facarvalho/MeetingHub-4/v2/docs/relatorio-validacao-v2.html

Dossiê de engenharia · Hardware

# MeetingHub-4 v2

Validação elétrica completa e autorização de fabricação da placa — roteador analógico de áudio/microfone para salas com 4 notebooks.

Revisão rev-10 Data 2026-09-04 Placa 2 camadas · 100% THT · 0 SMD Dimensões 192 × 156 mm Peças 121

AUTORIZADO PARA FABRICAÇÃO rev-10

Os 27 testes automatizados passam (21/21 elétricos + 8/8 seletor one-hot + 6/6 mixer/mudo + 7/7 transiente de comutação), confirmados em dois motores de simulação independentes — um solver MNA próprio e ngspice 41 com modelos de datasheet dos componentes reais da BOM. DRC da placa: 0 erros. As 3 falhas da v1 (que custaram R$ 3000) estão corrigidas e reverificadas. Liberação condicionada a 2 verificações de bancada no primeiro artigo (§9).

27/27

testes automatizados aprovados

0

erros de DRC · 0 pads não conectados

3/3

falhas da v1 corrigidas + reverificadas

2

motores de simulação concordam

## 1 · O equipamento

O MeetingHub-4 é uma caixa alimentada por USB-C que conecta um único headset a quatro notebooks em uma sala de reunião. O usuário ouve o áudio dos quatro laptops misturado (cada um com seu volume, mais um volume geral) e escolhe, por botão, para qual laptop o microfone do headset fala. Toda a comutação de microfone é feita por relés em lógica one-hot exclusiva (nunca dois ao mesmo tempo), e a placa liga sempre em mudo.

A arquitetura é deliberadamente analógica: um plugue TRRS não pode re-enumerar, entrar em suspend nem trocar o dispositivo padrão do Windows — que é exatamente a falha "o Windows perdeu meu headset no meio da call" que motivou o projeto. Não há firmware, não há USB de dados, nada para instalar.

Parâmetro | Valor (simulado / de projeto)
Alimentação | USB-C, somente VBUS · fusível PTC 500 mA (RXEF050) · TVS P6KE6.8A
Consumo total | 50,6 mA (10% do fusível) · só 1 relé energizado por vez
Entradas de laptop | 4 × TRRS 3,5 mm (PJ-3200B-4A, 100% THT)
Saída de headset | 1 × TRRS 3,5 mm (fone L/R + microfone electret)
Referência VBIAS | 2,5000 V · bufferizada (LM358) · Zsaída < 1 Ω
Mixer | NJM4580 somador inversor · −0,33×/canal · sem clip com 4 laptops em fase
Amp de fone | NJM4556A (70 mA) · ganho 2× · R16/R20 = 10 Ω série (rev-10)
Ganho monitor (carga 32 Ω) | 0,50× (−6 dB) · ~0,7 mW · ≈ 96 dB SPL em IEM
Resposta em frequência | −0,7 dB @ 100 Hz · plana até 20 kHz · −3 dB @ 44 Hz
Seletor de microfone | CD4043B (latch NOR) + matriz de 20 diodos + POR + 4 × 2N7000 → relés
Power-on reset | janela de mudo de 139 ms (garante boot em mudo mesmo com rampa lenta de VBUS)

## 2 · As três falhas da v1 — status na v2

A primeira fabricação (lote JLCPCB W2026080810364558) trouxe três erros de esquemático. Todos foram corrigidos na v2 e reverificados independentemente por simulação neste dossiê.

# | Falha da v1 | Correção na v2 | Reverificado em

1 | Potenciômetros de volume invertidos → direção errada, não zeravam | Sinal no terminal 3/6, VBIAS no 1/4. Full-CW = mais alto; full-CCW = silêncio. | §B2, §M — 80 dB de faixa
2 | Relés de mic K1–K4: bobina e contatos trocados → mic morto | Bobina = pinos 2 (+5 V) e 9 (dreno do MOSFET); D2–D5 freewheel corretos. Re-arquitetado one-hot. | §E, §G2 — exclusivo 8/8
3 | VBIAS sem buffer (10k/10k + 10 µF) → vazamento no volume mínimo | Buffer LM358 com realimentação após R38 → 2,5000 V exatos, < 1 Ω. | §A1–A4 — 0,5 mΩ

## 3 · Metodologia de simulação

LTspice é ferramenta Windows GUI e não roda neste ambiente headless. Foram usados dois motores independentes, com resultados que concordam em todos os números:

- Solver MNA próprio (simulation/scripts/mna.py) — análise nodal modificada com .op / .ac / .tran, solves complexos exatos sem erro de passo temporal. Cobre §A–§M (ganho, mudo, resposta, impedância).
- ngspice 41 com modelos de datasheet dos componentes reais da BOM — macromodelos de 2 polos para NJM4580 / NJM4556A / LM358 (GBW, slew, Avol, Vsat-vs-trilho, Iq), 1N4148, 2N7000 (VTO 2,1 V, Rds(on) 1,8 Ω), P6KE6.8A, CD4043B (modelo comportamental de latch NOR, limiares CD4000B em 5 V), relé G5V-1 (167 Ω + L, contato comutado). Netlists em simulation/spice/*.cir.
- Lógica one-hot — simulação de eventos construída diodo a diodo a partir do netlist (select_logic.py).
- Cada bloco também tem netlist LTspice equivalente em simulation/ltspice/ para reproduzir os números em LTspice real.

Valores e conectividade vêm de hardware/PCB/MeetingHub-4-v2.net e das folhas KiCad POWER / MIXER / HPAMP / SELECT_LOGIC — não do texto de projeto. Toolchain reprodutível: bash /home/fac/.simtools/regen_sim.sh.

## 4 · Placar de resultados

21/21

§A–§G · elétrico idealizado (MNA)

8/8

§E · sequência do seletor one-hot

6/6

§M · mixer / "volume zero é silêncio"

7/7

§O · comutar mic não interrompe o monitor

✓

§N · ngspice + modelos reais bate com MNA

1,25 V

§P · laptop deselecionado ainda "vê" o mic

### Resultados por bloco (§A–§G, motor MNA)

# | Requisito | Medido

A1 | VBIAS = 2,50 V | 2,5000 V | OK
A2 | Zsaída < 1 Ω (degrau de carga DC) | 0,5 mΩ | OK
A3/A4 | Zout < 1 Ω @ 1 kHz · < 5 Ω @ 20 kHz | 48 mΩ · 0,86 Ω | OK
B1 | ganho de sistema (nota de projeto ≈ 0,66×) | 0,659× sem carga · 0,50× (−6 dB) em 32 Ω (rev-10) | OK
B2 | direção do pote: CW alto, full-CCW = mudo | faixa ≥ 66 dB CW-vs-CCW | OK
B3 | 100 Hz – 20 kHz plano ±1 dB | −0,7 dB @ 100 Hz · +0,0 dB @ 20 kHz | OK
B4 | extensão de graves | −3 dB @ 44 Hz · −10 dB @ 20 Hz (ok para voz) | OK
C1 | ganho por canal −0,33 (−3k3/10k) | 0,330× | OK
C2/C3 | sem clip: 1 laptop · 4 laptops em fase (pior caso) | 0,15 Vpk · 0,59 Vpk / ±1,3 V (45%) | OK
D1 | ganho do amp de fone antes da rede de saída | 1,52× após divisor 10 Ω/32 Ω (rev-10) | OK
D2 | sem DC no fone (C17 bloqueia) | 0,0 mV | OK
D3 | cap de saída suficiente (C17 = 220 µF) | 22,6 Hz para C17/32 Ω | OK
D4 | > 0,5 mW em 32 Ω de uma fonte −10 dBV | 0,65–0,79 mW · +5,5 dB (rev-10; era 0,22 mW ❌ com 47 Ω) | OK
D5 | back-check: R16/R20 = 47 Ω (valor antigo) | 0,22 mW — confirma que a mudança rev-10 é o que traz o nível | OK
F1 | RST mantido ≥ 20 ms (boot em mudo com rampa lenta) | 139 ms | OK
F2 | sem reset residual após estabilizar | 0 mV | OK
G1 | corrente total < 500 mA | 50,6 mA (10%) | OK
G2 | só 1 relé energizado por vez | latch NOR one-hot (tabela-verdade) | OK
G3 | clamp de VBUS 6–8 V atrás do fusível | P6KE6.8A · Vbr 6,45–7,14 V | OK

### Cross-check ngspice + modelos reais (§N)

Grandeza | MNA idealizado | ngspice + BOM
VBIAS DC | 2,5000 V | 2,4999 V | =
Ganho @ 1 kHz em 32 Ω (rev-10) | 0,50× (−6,0 dB) | 0,456× (−6,8 dB) | =
Resposta @ 20 Hz / 100 Hz | −10,3 / −0,7 dB | −10,3 / −0,6 dB | =
Ganho do mixer por canal | 0,330× | 0,300× | =
Swing do mixer, 4 × −10 dBV em fase | ±0,59 V / ±1,3 V | ±0,78 V / ±1,1 V (70%) | sem clip
Sequência one-hot SW2→SW5 | Q1→Q2→Q3→Q4 exclusivo | idêntico, lógica 4,98 V | =
PORN @ 100 ms | > 2,5 V | 3,20 V (RST mantido) | =
Roteamento de mic após seleção | só o laptop selecionado | selecionado 37 mV pp · outros 0,4 µV | =

## 5 · Alteração da rev-10 — nível no fone

O único teste que reprovava (D4) tinha uma causa única: R16/R20 = 47 Ω ficam fora da malha de realimentação de U2A, formando com um headset de 16–32 Ω um divisor 47/(47+32) ≈ 0,4. A correção é trocar dois resistores por 10 Ω — mesmo footprint, mesma posição, mesma rotação. O netlist continua byte-idêntico (95 nets, conjuntos de nós verificados iguais): sem re-roteamento, Gerbers/furação/CPL inalterados; mudam só o PDF do esquemático e as 3 BOMs.

| rev-9 (47 Ω) | rev-10 (10 Ω)
Ganho de sistema em 32 Ω | 0,27× (−11,5 dB) | 0,50× (−6 dB)
Potência em 32 Ω (fonte −10 dBV) | 0,22 mW | 0,65–0,79 mW (+5,5 dB)
SPL estimado (IEM 100 dB/mW) | ≈ 86 dB | ≈ 96 dB
Proteção de curto (NJM4556A, limite interno 70 mA) | boa | mantida — 10 Ω ainda limita curto no jack; estágio incondicionalmente estável (.ac sem peaking)

R38 (isolação do buffer VBIAS) permanece 47 Ω — só R16 e R20 mudam. Peça: UNI-ROYAL MFR0W4F100JA50 = LCSC C57437 — 10 Ω 1/4 W filme metálico ±1% ±50 ppm, D2,2 × 6,5 mm, ~10 800 em estoque JLC (restaura o padrão filme-metálico ±1% que a peça de 47 Ω já tinha).

## 6 · Inspeção da placa (DRC / ERC)

DRC headless com o projeto carregado (SETTINGS_MANAGER.LoadProject + regra .kicad_dru para o footprint USB-C):

Item | Resultado
Erros de DRC | 0
Pads não conectados | 0 — placa 100% roteada (902 seg / 35 vias)
Erros de footprint | 0
Avisos silk_over_copper | 5 — refs RV1–RV5 na borda da placa; o KiCad apara o silk no contorno ao plotar (cosmético)
Pads SMD | 0 — verificado pad a pad
Clearances internos do J1 (USB-C) | passam na netclass 0,15 mm (mesmo valor da v1 fabricada; piso JLCPCB 0,127 mm)

A revisão de esquemático em 3 passes (DC/bias · áudio com 4 laptops · roteamento de mic e lógica one-hot) confirmou: pinos de alimentação de todos os CIs, tabela-verdade do latch para cada botão e para o gesto de 2 botões, polaridade dos diodos freewheel, e mapeamento dos contatos dos relés (rev-9).

## 7 · Formas de onda & respostas simuladas

Resposta em frequência do canal de monitoração

Canal de monitoração — resposta em frequência. Plana dentro de ±1 dB em 100 Hz–20 kHz. Corte de −3 dB em 44 Hz (capacitores de acoplamento de 1 µF) — adequado para voz (300–3400 Hz). Carga de 32 Ω vs alta impedância.

Ganho da cadeia completa carregado vs sem carga, rev-10

Cadeia completa — ganho carregado vs sem carga (rev-10, R16/R20 = 10 Ω). O ganho em 32 Ω sobe de 0,27× para 0,50× com a troca dos resistores de saída.

Lei de mudo dos potenciômetros de volume

"Volume zero é silêncio?" Esta era a falha da v1. Com o pote no mínimo o cursor fica em VBIAS através de ~0 Ω — saída em −66 dB (42 µV) para uma entrada de 0,316 Vrms. Mesmo no pior caso de resistência residual do pote (50 Ω) → −46 dB, inaudível.

Sequência do seletor one-hot de microfone

Seletor one-hot — sequência de botões. Liga em mudo (POR segura todos os RST por ~140 ms); cada toque em SW2…SW5 seleciona um laptop e libera os outros três; SW3+SW4 juntos = mudo, e permanece mudo ao soltar.

Temporização do power-on reset

Power-on reset. C24 (10 µF) acopla o degrau de +5 V a PORN; R37 (100 k) descarrega. Enquanto PORN > Vih do CD4043B, todos os RST ficam altos → Q1…Q4 = 0 → nenhum relé → mic mudo por 139 ms, folga larga sobre o piso de 20 ms.

Comutar o microfone não interrompe o monitor (§O). Um tom de 1 kHz atravessa a cadeia completa enquanto o latch comuta K1→K2. Variação de amplitude no fone: 0,02%. Pior glitch < 80 µV (−63 dB). O trilho de +5 V não afunda — os diodos freewheel devolvem a energia da bobina como um bump positivo.

## 8 · Estado de integração — microfone do laptop deselecionado (§P)

Pergunta original: "laptop 1 com mic ativo, mudo para o laptop 2. O SO do laptop 1 acha que o mic está ligado ou desligado?" Um codec classifica o jack pela tensão DC que lê no sleeve do mic. Na rev-9 os contatos foram religados para que um laptop deselecionado veja 2,2 kΩ → GND (R39–R42):

Cenário | DC no sleeve | Veredito do codec
Laptop selecionado (electret real ~2 kΩ) | 1,19 V | headset mic presente
Laptop deselecionado — NC → 2,2 kΩ (rev-9/10) | 1,25 V | headset mic presente (silêncio)
NC aberto (rev-8, antigo) | 2,50 V | "sem microfone" ⚠️
NC → GND direto | 0,001 V | dispara media-key ⚠️

Não existe sinal analógico num jack TRRS que signifique "mudo" para um SO — mudo de mic no Windows é função de software/HID. Com a correção, o mudo é funcional, não sinalizado: o endpoint de mic do laptop deselecionado continua presente e o outro lado apenas não recebe áudio. A metade do SO (firmware do codec) ainda deve ser verificada em bancada nos laptops-alvo.

## 9 · Pendências antes de ordenar (não são problemas de projeto)

Duas verificações de bancada no primeiro artigo. A BOM está completa e toda em estoque JLCPCB.

1. Convenção de terminais do potenciômetro Alps RK09712200HA — obrigatório. Com o knob totalmente em anti-horário, o cursor (terminal 2) deve dar ≈ 0 Ω ao terminal 1. O netlist está fiado corretamente para essa convenção; a simulação não pode verificar o pote físico. Se medir ao contrário, é troca de fio (RVn.1↔RVn.3), não respin. É exatamente a classe da falha #1 da v1 — não pule.
2. Comportamento do SO com mic deselecionado — testar nos laptops-alvo. O lado da placa está correto (§P, 1,25 V); a reação do codec é firmware.

Nenhuma das duas é um bloqueio de projeto — são verificações de primeiro artigo de bancada, padrão para qualquer lançamento. O R16/R20 de 10 Ω da rev-10 usa UNI-ROYAL MFR0W4F100JA50 / LCSC C57437 (filme metálico ±1%, ~10 800 em estoque JLC); alternativa drop-in Yageo MFR-25JT-52-10R (C176452).

## 10 · Arquivos de fabricação

Arquivo | Conteúdo | Mudou na rev-10?
Gerbers/…-Gerbers.zip | 2 camadas F/B + máscara + silk + Edge.Cuts | não (netlist idêntico)
Gerbers/…-.drl | furação (35 vias + furos de pino) | não
Gerbers/…-CPL.csv | pick-and-place, formato JLCPCB, rotação corrigida por footprint | não (R16/R20 mesma posição)
BOM/BOM-JLC-…csv | BOM formato nativo JLC para montagem | sim — R16/R20 → 10 Ω
BOM/BOM-PCBA-…csv | BOM detalhada (LCSC, MPN, notas) | sim
Schematics/…-Schematic.pdf | esquemático 6 folhas | sim — regenerado

Placa: 192 × 156 mm, cantos R6, 6 × M3. Frente = RV1–5 / SW2–5 / J6 (headset). Traseira = J1 (USB-C) + J2–5 (laptops). Gabinete = 2 chapas de acrílico (topo + base), laterais abertas.

### Estoque JLCPCB — snapshot 2026-09-04

Toda a BOM (25 linhas, 121 peças) está em estoque de montagem JLCPCB. Cinco itens têm estoque baixo e devem ser conferidos / pré-reservados na hora do pedido — eles limitam o tamanho do lote:

Peça | Ref. | Estoque | Lotes de ~1 placa
Alps RK09712200HA (C470545) | RV1–RV5 (5×/placa) | 175 | ~35 placas — o limitante
NJM4556AD (C2838125) | U2 (amp de fone) | 169 | ~169
P6KE6.8A TVS (C152132) | D1 | 33 | ~33 — muito baixo
CD4043BE (C22390239) | U4 (seletor) | 488 | ~488
NJM4580DD (C5184871) | U1 (mixer) | 491 | ~491

Para D1 (TVS): qualquer TVS unidirecional 600 W com VBR 6–8 V em DO-15 serve (ex.: 1.5KE6.8A) — mesma função, mesmo footprint. Para os CIs e o pote, prefira pré-reservar a peça exata; substitutos pin-compatíveis existem mas exigem reconferência de bancada. Demais peças com folga (> 1000 un.): resistores, 1N4148, 2N7000, relé G5V-1, LM358, jacks PJ-3200B-4A, eletrolíticos, USB-C, fusível, botões.

Revisão de engenharia eletrônica / mecatrônica — simulação e inspeção

Dois motores de simulação independentes · DRC/ERC · revisão de esquemático em 3 passes. Recomendação: liberar para fabricação a rev-10, executando as 2 verificações do §9 no primeiro artigo.

MeetingHub-4 v2 · rev-10 · 2026-09-04. Gerado a partir de v2/docs/v2-simulation-validation.md, CHANGELOG.md e da re-execução completa de simulation/. Plots: motor MNA + ngspice 41 (matplotlib, backend Agg). Reprodutível via bash /home/fac/.simtools/regen_sim.sh.
