facarvalho/MeetingHub-4/v2/box/mh4-arte-chapa-topo.pdf

MH1 | MH2
MH3 | MH4
MH5 | MH6

USB-C 5V

PC 1 | PC 2
PC 3 | PC 4
MeetingHub-4 | GERAL

SELECT

## MeetingHub-4 v2 — Arte para a chapa topo (192,00 × 156,00 mm)

Cena reproduzida da animação de v2/docs/manual-uso-v2.html (tema escuro).
A chapa topo da v2 é lisa (sem furo de trimmer) — esta arte é só identidade visual, não funcional.

## IMPRIMIR EM TAMANHO REAL / 100%

desative "ajustar à página" / "fit to page" / "escalar" na caixa de impressão. Calibração — 50,00 mm

meça esta barra com uma régua depois de imprimir

Se não medir exatamente 50,00 mm, a impressão foi escalada — corrija a impressora antes de recortar ou colar esta arte na chapa. As posições de MH1–MH6 nesta folha são as mesmas do plano de corte

(mh4-plano-de-corte.pdf) e do arquivo mh4-acrilico-topo.dxf.

MeetingHub-4 v2 · arte da chapa topo · cena de v2/docs/manual-uso-v2.html (4 notebooks + headset + caixa) MH1–MH6 = fixação M3 · baseado em v1/box/mh4-arte-chapa-topo.pdf
