facarvalho/MeetingHub-4/v1/box/mh4-arte-chapa-topo.pdf

## MeetingHub-4 — Arte para a chapa topo (160,09 × 133,96 mm)

Escala 1:1 — mesma geometria de mh4-acrilico-topo.dxf. Imprimir e colar na chapa antes ou depois do corte.

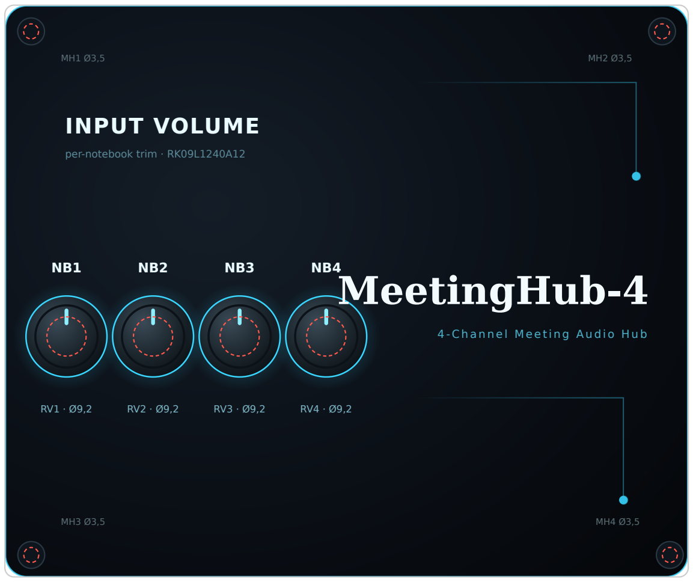
[picture p1: figure]
INPUT VOLUME; per-notebook trim · RK09L1240A12; MeetingHub-4; 4-Channel M eeting Audi o H ub

IMPRIMIR EM TAMANHO REAL / 100% — desative "ajustar à página" / "fit to page" /

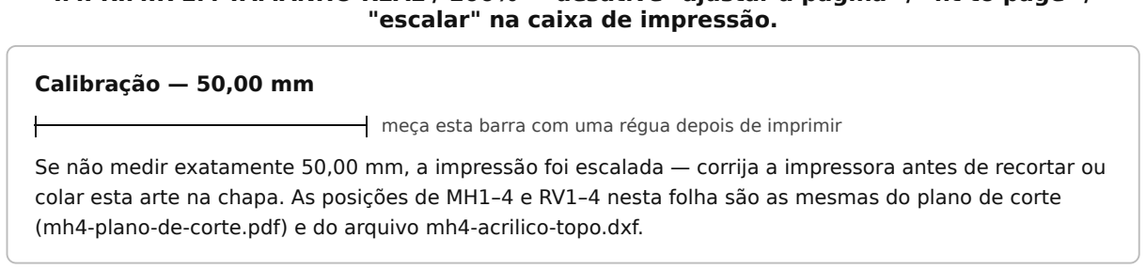
[picture p2: figure]
"escalar" na caixa de impressão.; Calibração — 50,00 mm; (mh4-plano-de-corte.pdf) e do arquivo mh4-acrilico-topo.dxf.

meça esta barra com uma régua depois de imprimir Se não medir exatamente 50,00 mm, a impressão foi escalada — corrija a impressora antes de recortar ou colar esta arte na chapa. As posições de MH1–4 e RV1–4 nesta folha são as mesmas do plano de corte

MeetingHub-4 · arte da chapa topo · RV1–4 = trim de volume por notebook (NB1–4) · MH1–4 = fixação M3
