facarvalho/MeetingHub-4/v1/box/mh4-paineis-frontal-traseiro.pdf

# MeetingHub-4 — Painel TRASEIRO (elevação, X real / Z estimado)

X = posição real (MeetingHub-4.kicad_pcb). Z = altura acima da base do gabinete, ESTIMADA — ver tabela.

⚠ ESTA FOLHA NÃO É GABARITO DE CORTE. As alturas (Z) são estimativas de mercado, não medidas reais do componente físico. Confirme com paquímetro

superfície da PCB

base do gabinete (Z=0)

J1

X=111.04

J2

X=17.45

X=30.45

J4

X=43.45

X=56.45

REF. | X (MM) | Z ESTIMADO (MM, DA BASE) | FUNÇÃO | ORIGEM DA ESTIMATIVA DE Z
J1 | 111.04 | 18.50 | USB-C · alimentação 5V | 3,9mm lido no desenho GCT USB4085 (Seção A-A) — folha do fabricante
J2 | 17.45 | 20.60 | NB1 | 6,0mm — valor típico de mercado p/ jack P3 horizontal deste porte, NÃO confirmado em datasheet específico
J3 | 30.45 | 20.60 | NB2 | 6,0mm — valor típico de mercado p/ jack P3 horizontal deste porte, NÃO confirmado em datasheet específico
J4 | 43.45 | 20.60 | NB3 | 6,0mm — valor típico de mercado p/ jack P3 horizontal deste porte, NÃO confirmado em datasheet específico
J5 | 56.45 | 20.60 | NB4 | 6,0mm — valor típico de mercado p/ jack P3 horizontal deste porte, NÃO confirmado em datasheet específico

MeetingHub-4 · painel traseiro · envelope do gabinete: 0–26.8mm · superfície da PCB em Z=14.6mm

## MeetingHub-4 — Painel FRONTAL (elevação, X real / Z estimado)

X = posição real (MeetingHub-4.kicad_pcb). Z = altura acima da base do gabinete, ESTIMADA — ver tabela.

⚠ ESTA FOLHA NÃO É GABARITO DE CORTE. RV5 é a estimativa menos confiável desta folha (10mm de saliência é um palpite, não veio de datasheet).

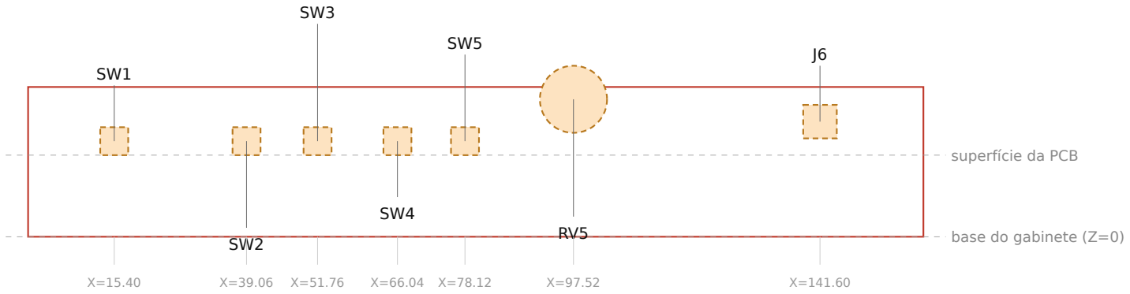
[picture p3: figure]
superfície da PCB; base do gabinete (Z=0)

REF. | X (MM) | Z ESTIMADO (MM, DA BASE) | FUNÇÃO | ORIGEM DA ESTIMATIVA DE Z
SW1 | 15.40 | 17.10 | mudo (provável) | 2,5mm — metade dos 5mm de altura do corpo (SHOU HAN TS665ZJ, LCSC C557599, fonte real) — centro do atuador é estimado
SW2 | 39.06 | 17.10 | seletor mic | 2,5mm — metade dos 5mm de altura do corpo (SHOU HAN TS665ZJ, LCSC C557599, fonte real) — centro do atuador é estimado
SW3 | 51.76 | 17.10 | seletor mic | 2,5mm — metade dos 5mm de altura do corpo (SHOU HAN TS665ZJ, LCSC C557599, fonte real) — centro do atuador é estimado
SW4 | 66.04 | 17.10 | seletor mic | 2,5mm — metade dos 5mm de altura do corpo (SHOU HAN TS665ZJ, LCSC C557599, fonte real) — centro do atuador é estimado
SW5 | 78.12 | 17.10 | seletor mic | 2,5mm — metade dos 5mm de altura do corpo (SHOU HAN TS665ZJ, LCSC C557599, fonte real) — centro do atuador é estimado
RV5 | 97.52 | 24.60 | volume master | 10,0mm — estimativa por comparação com potenciômetros de porte semelhante — RV5 é o menos confiável desta folha
J6 | 141.60 | 20.60 | headset | 6,0mm — valor típico de mercado p/ jack P3 horizontal deste porte, NÃO confirmado em datasheet específico

MeetingHub-4 · painel frontal · envelope do gabinete: 0–26.8mm · superfície da PCB em Z=14.6mm
