facarvalho/MeetingHub-4/v1/box/mh4-plano-de-corte.pdf

# MeetingHub-4 — Plano de Corte e Furação — Acrílico

Corte a laser · acrílico (PMMA) 3 mm · origem das coordenadas: MeetingHub-4.kicad_pcb (validado) · revisão A

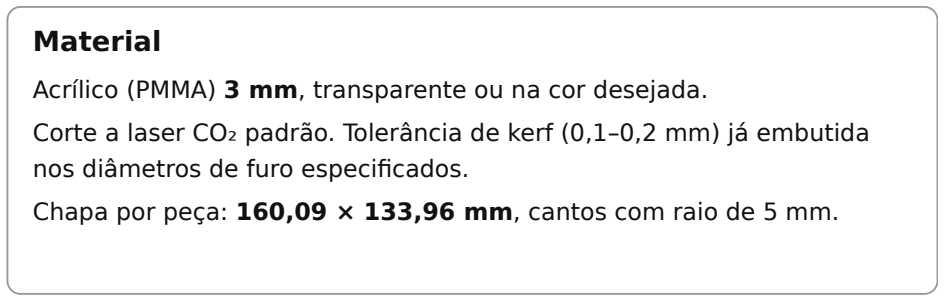
[picture p4: figure]
Material; nos diâmetros de furo especificados.

Acrílico (PMMA) 3 mm, transparente ou na cor desejada.
Corte a laser CO₂ padrão. Tolerância de kerf (0,1–0,2 mm) já embutida

Chapa por peça: 160,09 × 133,96 mm, cantos com raio de 5 mm.

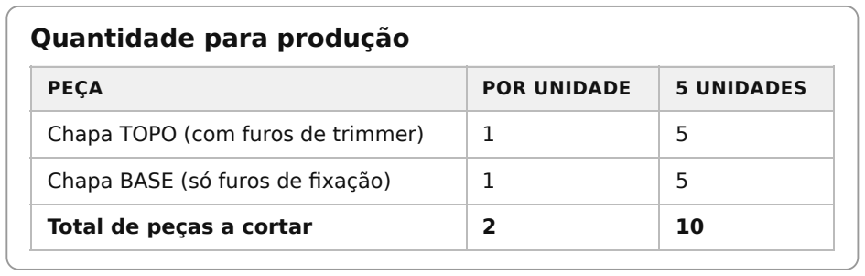
[picture p5: figure]
Quantidade para produção; PEÇA; POR UNIDADE; 5 UNIDADES; Chapa TOPO (com furos de trimmer); Chapa BASE (só furos de fixação); Total de peças a cortar

### Arquivos desta entrega

ARQUIVO | CONTEÚDO | USO
mh4-acrilico-topo.dxf | contorno + 4 furos M3 + 4 furos de trimmer Ø9,2 | enviar direto para a máquina de corte
mh4-acrilico-base.dxf | contorno + 4 furos M3 | enviar direto para a máquina de corte
mh4-acrilico-topo.svg / -base.svg | mesmas geometrias, formato vetorial alternativo | conferência visual / oficinas que preferem SVG
mh4-prova-1-1.pdf | as duas chapas em escala 1:1, numa folha A4 | imprimir e conferir antes de mandar cortar de verdade
este PDF | desenho cotado + tabela de furos + lista de material + kit de fixação (anexo) | conferência humana e pedido de orçamento

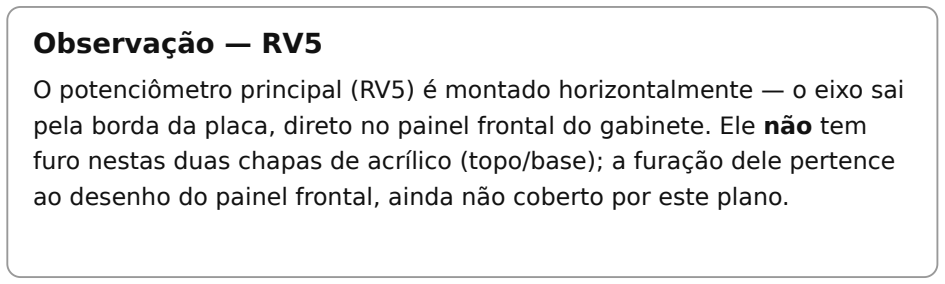
[picture p6: figure]
Observação — RV5

O potenciômetro principal (RV5) é montado horizontalmente — o eixo sai pela borda da placa, direto no painel frontal do gabinete. Ele não tem furo nestas duas chapas de acrílico (topo/base); a furação dele pertence ao desenho do painel frontal, ainda não coberto por este plano.

### Observação — porca de barril

Porca de barril M3 (15–20 mm) embutida na chapa topo, furo Ø3,2– 3,5 mm. Ela pode girar ao apertar — trave com um alojamento hexagonal raso (6,2 mm entre faces, 1,0–1,5 mm fundo, exige fresa/rebaixo) ou segure com um alicate na primeira volta. Kit completo de referência na última página.

MeetingHub-4 · plano de corte gerado a partir do MeetingHub-4.kicad_pcb · datum (0,0) = canto superior esquerdo de cada chapa

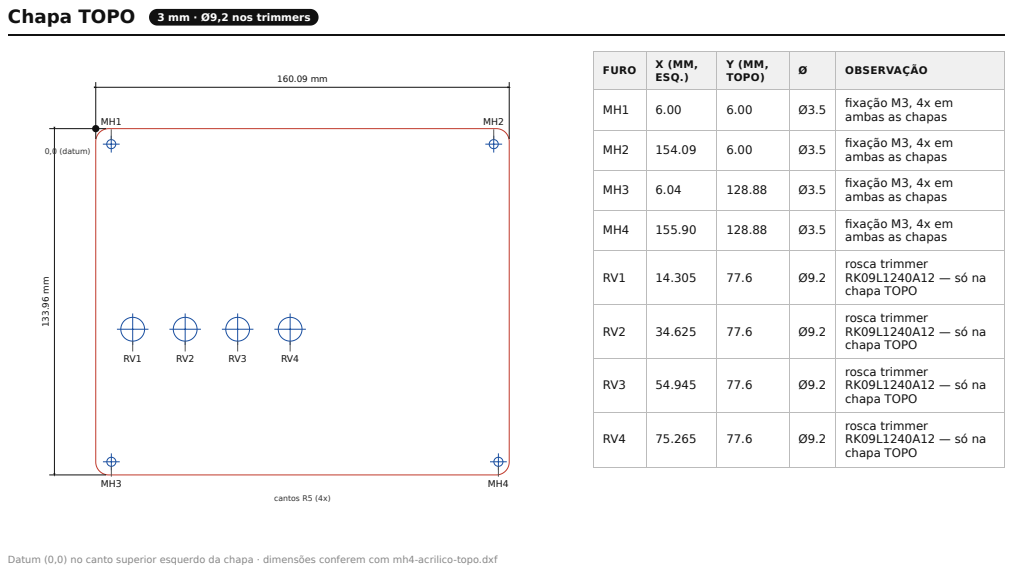
[picture p7: page 2]
0,0 (datum); cantos R5 (4x)

Chapa TOPO 3 mm · Ø9,2 nos trimmers

FURO | X (MM, ESQ.) | Y (MM, TOPO) | Ø | OBSERVAÇÃO

MH1 | 6.00 | 6.00 | Ø3.5 | fixação M3, 4x em ambas as chapas

MH2 | 154.09 | 6.00 | Ø3.5 | fixação M3, 4x em ambas as chapas

MH3 | 6.04 | 128.88 | Ø3.5 | fixação M3, 4x em ambas as chapas

MH4 | 155.90 | 128.88 | Ø3.5 | fixação M3, 4x em ambas as chapas

RV1 | 14.305 | 77.6 | Ø9.2 | rosca trimmer RK09L1240A12 — só na chapa TOPO

RV2 | 34.625 | 77.6 | Ø9.2 | rosca trimmer RK09L1240A12 — só na chapa TOPO

RV3 | 54.945 | 77.6 | Ø9.2 | rosca trimmer RK09L1240A12 — só na chapa TOPO

RV4 | 75.265 | 77.6 | Ø9.2 | rosca trimmer RK09L1240A12 — só na chapa TOPO

Datum (0,0) no canto superior esquerdo da chapa · dimensões conferem com mh4-acrilico-topo.dxf

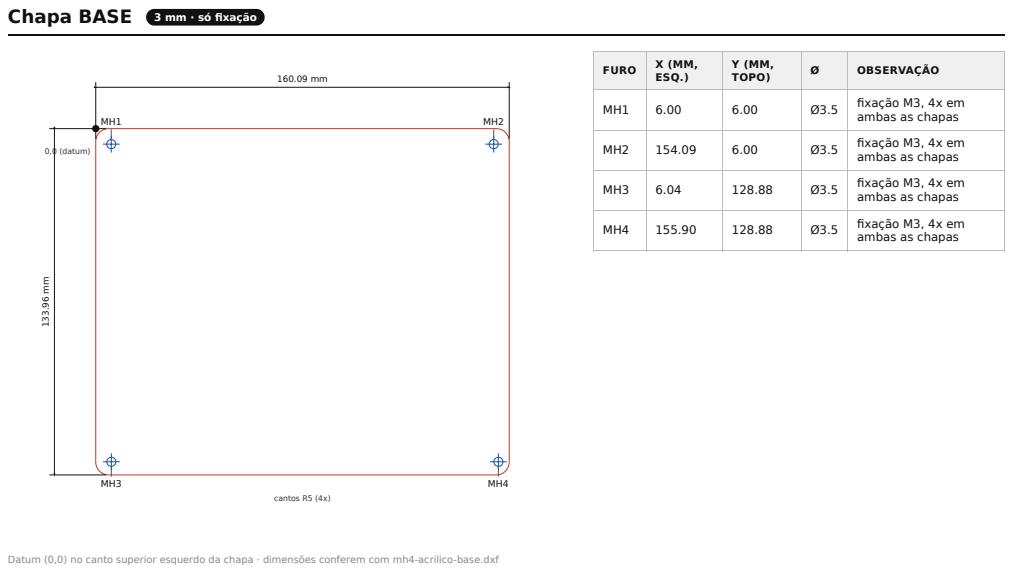
[picture p8: page 3]
0,0 (datum); cantos R5 (4x)

Chapa BASE 3 mm · só fixação

FURO | X (MM, ESQ.) | Y (MM, TOPO) | Ø | OBSERVAÇÃO

MH1 | 6.00 | 6.00 | Ø3.5 | fixação M3, 4x em ambas as chapas

MH2 | 154.09 | 6.00 | Ø3.5 | fixação M3, 4x em ambas as chapas

MH3 | 6.04 | 128.88 | Ø3.5 | fixação M3, 4x em ambas as chapas

MH4 | 155.90 | 128.88 | Ø3.5 | fixação M3, 4x em ambas as chapas

Datum (0,0) no canto superior esquerdo da chapa · dimensões conferem com mh4-acrilico-base.dxf

## Ferragem de montagem — 5 unidades

ITEM | POR UNIDADE | 5 UNIDADES | COMPRAR | OBSERVAÇÃO
Parafuso M3 cabeça chata, ~30 mm | 4 | 20 | 25 | cobre base + calço inferior + PCB + calço superior + rosca na porca de barril
Espaçador de nylon M3, furo passante, 10 mm | 4 | 20 | 25 | calço inferior — ajustar 10–15 mm conforme conector mais alto sob a placa
Espaçador de nylon M3, furo passante, 9,2 mm | 4 | 20 | 25 | calço superior — alinhado ao trimmer RK09L1240A12
Porca de barril M3 (hexagonal), 15–20 mm | 4 | 20 | 25 | embutida na chapa topo, recebe o parafuso vindo de baixo
Arruela Ø14×0,5 mm, furo Ø9,1 mm | 4 | 20 | 25 | 1 por trimmer (RV1–4)
Porca M9×0,75, 11 mm entre faces | 4 | 20 | 25 | 1 por trimmer (RV1–4)

### Ordem de montagem

1. Parafuso M3 pelo lado de baixo da chapa base → calço inferior (10 mm) → placa PCB → calço superior (9,2 mm) → chapa topo → aperta na porca de barril embutida, nos 4 cantos (MH1–MH4).
2. Encaixe os trimmers RV1–4 nos furos de Ø9,2 mm da chapa topo, coloque a arruela Ø14 e rosqueie a porca M9 por fora.
3. Nunca rosqueie parafuso direto no acrílico — sempre furo passante + espaçador/porca fazendo o aperto.
4. Ao apertar, a porca de barril pode girar junto — segure com um alicate na primeira volta, ou corte o alojamento hexagonal descrito na página 1 se quiser que ela trave sozinha.

MeetingHub-4 · plano de corte e furação · gerado para pedido de fabricação em 5 unidades

## Anexo — kit de fixação completo referência

Catálogo de peças, dimensões e vista explodida usados como referência para este plano — confirma as mesmas quantidades e medidas das páginas anteriores.

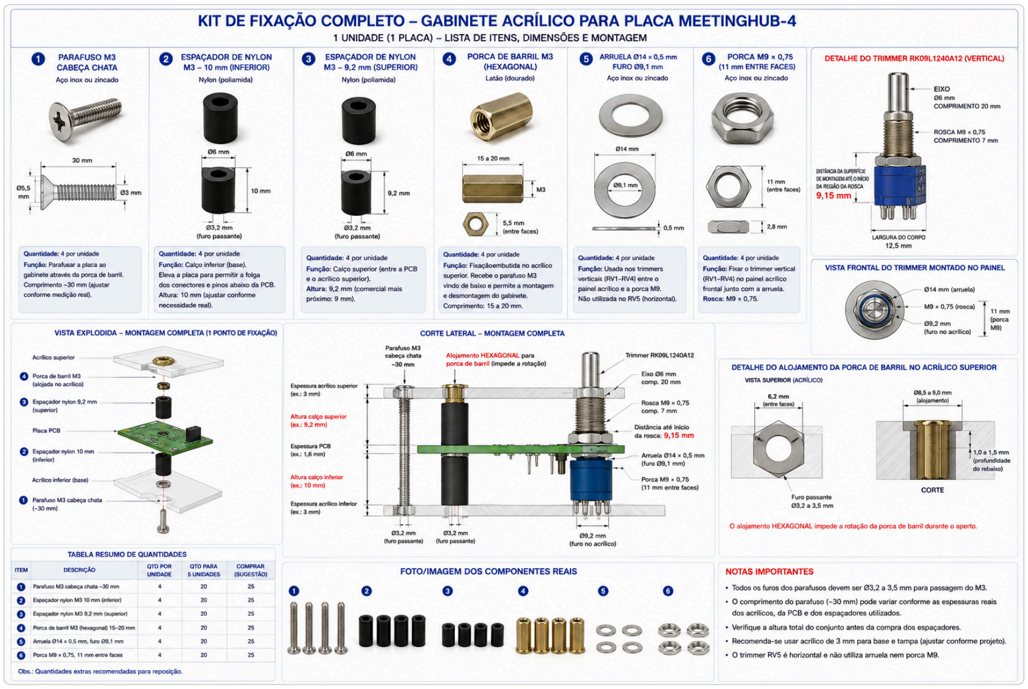
[picture p9: figure]
