facarvalho/MeetingHub-4/v1/hardware/BOM/BOM-001.md

# MeetingHub-4
# BOM-001 - Bill of Materials

Version: 0.1
Status: Draft

# 1. Connectors

## J1-J4 - Laptop Inputs

Quantity: 4

Type:
- 3.5mm female P2
- TRRS
- CTIA
- metallic
- panel mount

## J5 - Headset

Quantity: 1

Type:
- 3.5mm female P2
- TRRS
- CTIA
- metallic
- panel mount

# 2. Volume Control

## VR1-VR4

Function:
Individual laptop volume

Specification:
- Stereo potentiometer
- 10k ohms
- Logarithmic taper
- Metallic shaft

## VR5

Function:
Master volume

Specification:
- Stereo potentiometer
- 10k ohms
- Logarithmic taper

# 3. Audio Mixer

Candidate component:

NE5532

Quantity:
2

Function:
- Left channel summing amplifier
- Right channel summing amplifier

# 4. Headphone Amplifier

Candidate component:

NJM4556A

Function:
Driver for headset

# 5. Microphone

## Laptop selection

Method:
Signal relay

Candidates:

- Omron G6K
- Panasonic TQ2

Requirements:
- gold contact
- low resistance
- high durability

# 6. MUTE

Type:

Normally closed industrial pushbutton

Function:

Interrupt the microphone line

# 7. Power Supply

Input:

USB-C 5V

Protection:

- resettable fuse
- reverse polarity protection
- EMI filter

# 8. Passive Components

Resistors:

- 1%
- metal film

Capacitors:

- C0G/NP0 for critical audio
- low-ESR electrolytics on the power supply

# 9. Notes

All components should prioritize:

- availability;
- durability;
- ease of replacement;
- low noise.
